kbumsik/Nucleo2Arduino-Adapter/reference/nucleo_f401_arduino.png

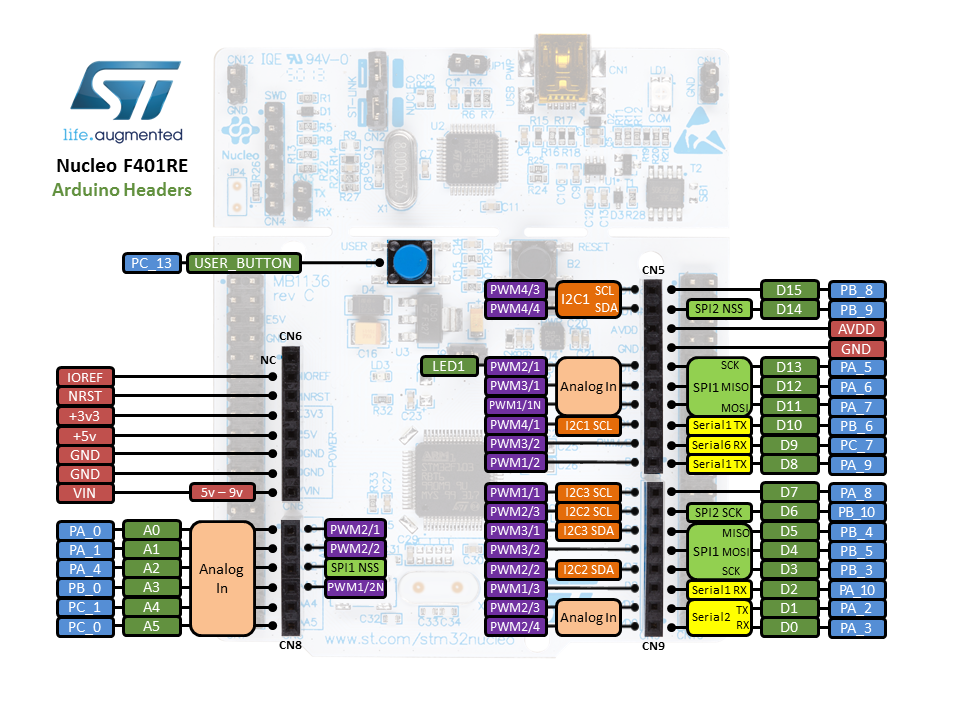
reference/nucleo_f401_arduino.png
